f0xxxxxy/esp32-canboard/main/src/i2c_master.c

#include "i2c_master.h"
#include "driver/i2c.h"
#include "esp_log.h"
#include "freertos/FreeRTOS.h"
#include "freertos/task.h"

static const char *TAG = "i2c_master";

/**
 * @brief Initialize the ESP-IDF I2C master driver on I2C_NUM_0.
 * @param sda_gpio SDA GPIO pin.
 * @param scl_gpio SCL GPIO pin.
 * @return true on success; false when parameter config or driver install fails.
 */
bool i2c_master_init(gpio_num_t sda_gpio, gpio_num_t scl_gpio)
{
    i2c_config_t conf = {
        .mode = I2C_MODE_MASTER,
        .sda_io_num = sda_gpio,
        .sda_pullup_en = GPIO_PULLUP_ENABLE,
        .scl_io_num = scl_gpio,
        .scl_pullup_en = GPIO_PULLUP_ENABLE,
        .master.clk_speed = 100000,
    };
    esp_err_t err = i2c_param_config(I2C_NUM_0, &conf);
    if (err != ESP_OK) {
        ESP_LOGE(TAG, "i2c_param_config failed: %d", err);
        return false;
    }
    err = i2c_driver_install(I2C_NUM_0, conf.mode, 0, 0, 0);
    if (err != ESP_OK) {
        ESP_LOGE(TAG, "i2c_driver_install failed: %d", err);
        return false;
    }
    // Small delay after I2C init improves peripheral readiness at boot.
    vTaskDelay(pdMS_TO_TICKS(300));
    return true;
}

/**
 * @brief Perform a combined I2C write-read transaction.
 * @param addr 7-bit target device address.
 * @param write_data Optional write buffer pointer.
 * @param write_len Number of bytes to write.
 * @param read_data Optional read buffer pointer.
 * @param read_len Number of bytes to read.
 * @return true when command sequence succeeds; false on I2C command failure.
 */
bool i2c_master_write_read(uint8_t addr, const uint8_t *write_data, size_t write_len, uint8_t *read_data, size_t read_len)
{
    i2c_cmd_handle_t cmd = i2c_cmd_link_create();
    i2c_master_start(cmd);
    i2c_master_write_byte(cmd, (addr << 1) | I2C_MASTER_WRITE, true);
    if (write_len) {
        i2c_master_write(cmd, (uint8_t *)write_data, write_len, true);
    }
    if (read_len) {
        i2c_master_start(cmd);
        i2c_master_write_byte(cmd, (addr << 1) | I2C_MASTER_READ, true);
        if (read_len > 1) {
            i2c_master_read(cmd, read_data, read_len - 1, I2C_MASTER_ACK);
        }
        i2c_master_read_byte(cmd, read_data + read_len - 1, I2C_MASTER_NACK);
    }
    i2c_master_stop(cmd);
    esp_err_t ret = i2c_master_cmd_begin(I2C_NUM_0, cmd, pdMS_TO_TICKS(100));
    i2c_cmd_link_delete(cmd);
    return (ret == ESP_OK);
}
